elliotnash/OSU-ECE342-Oscilloscope/docs/blocks/frontend/frontend-portrait.png

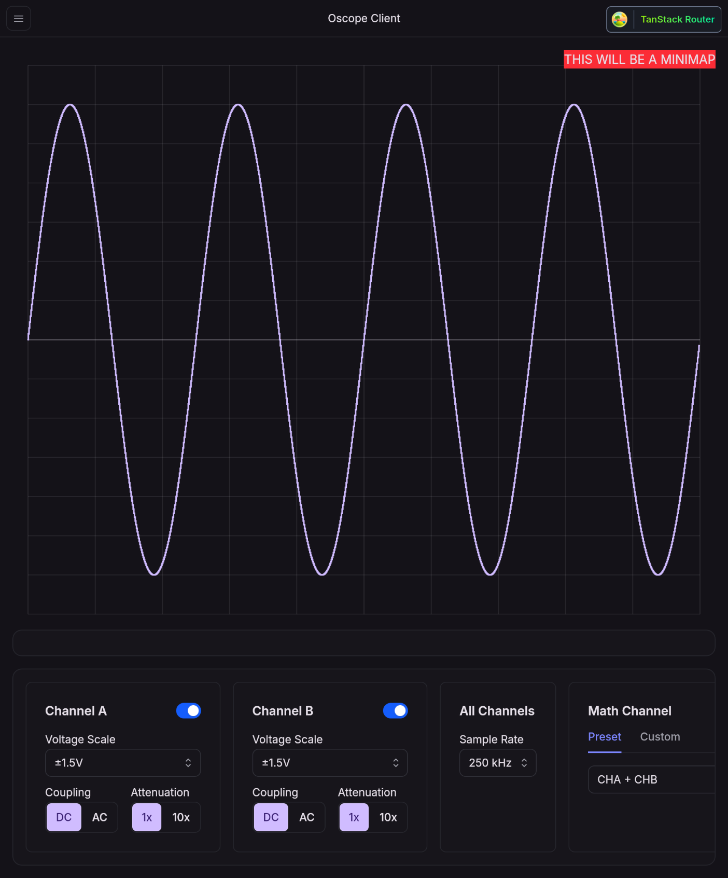
docs/blocks/frontend/frontend-portrait.png
