elliotnash/OSU-ECE342-Oscilloscope/docs/images/cover.jpeg

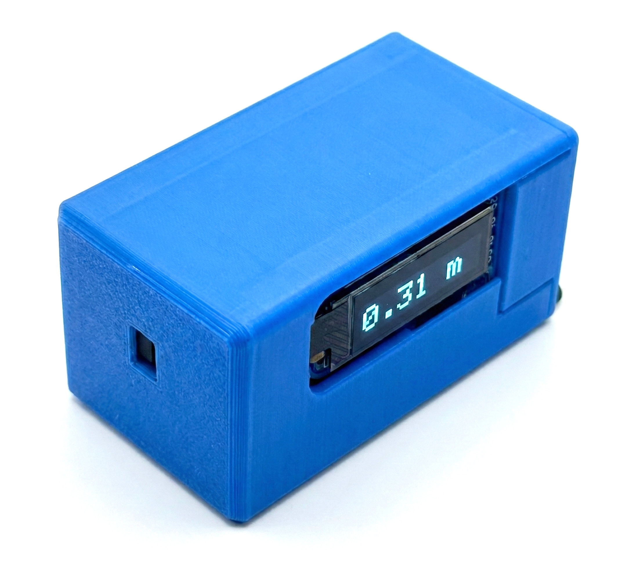
docs/images/cover.jpeg
