elliotnash/OSU-ECE342-Oscilloscope/docs/images/OscopeCaseTop.png

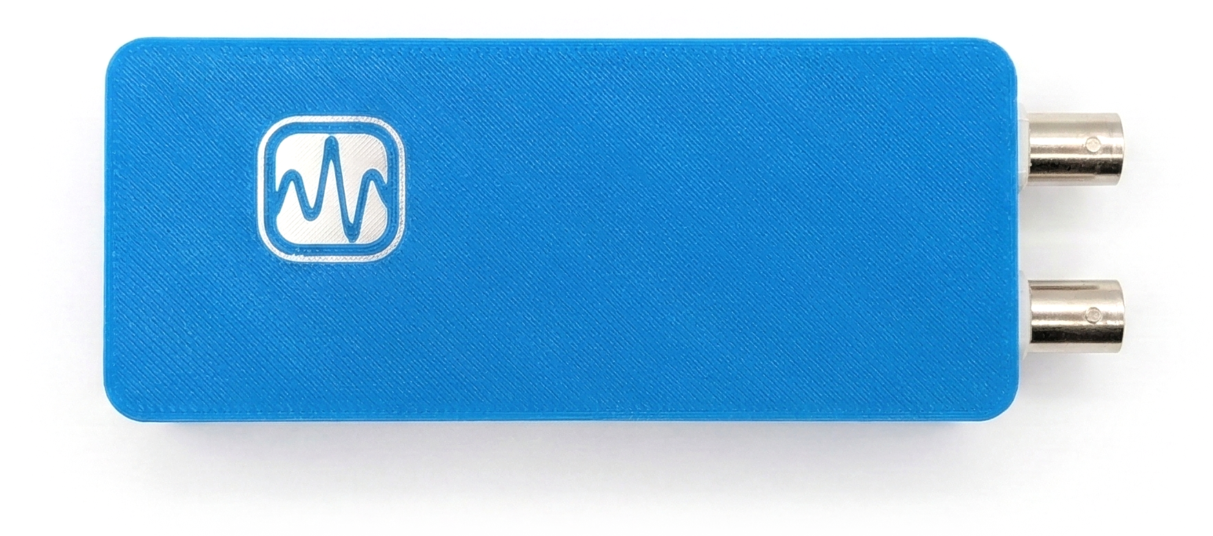
docs/images/OscopeCaseTop.png
