elliotnash/OSU-ECE342-Oscilloscope/docs/images/skeleton.jpeg

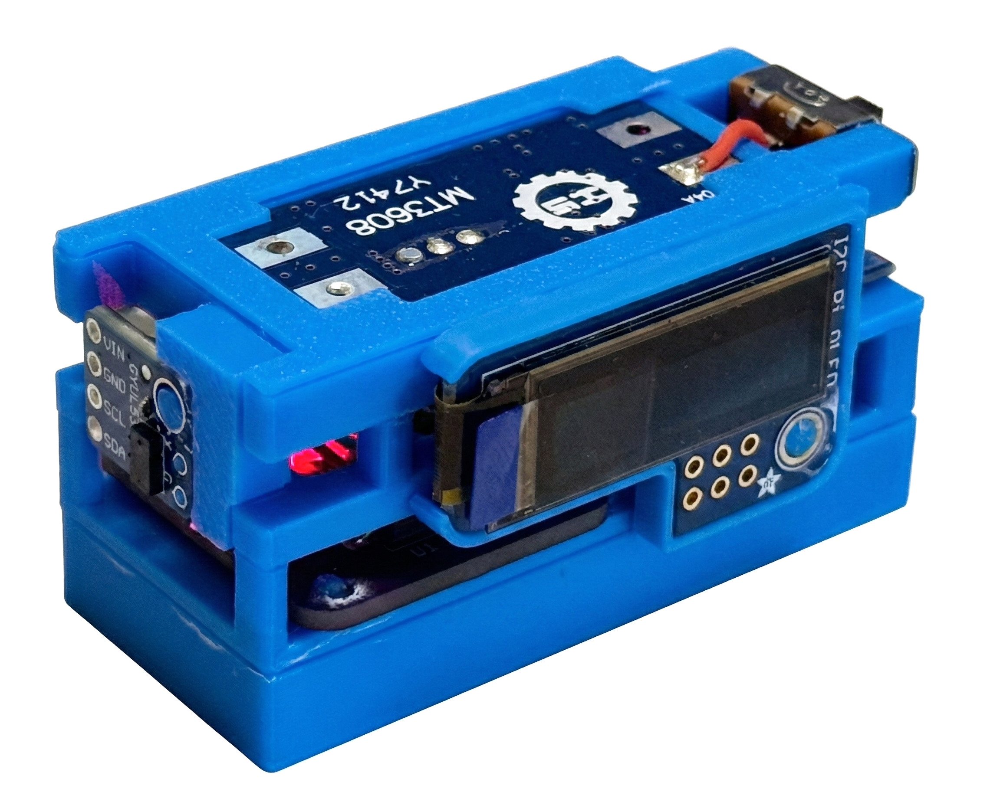
docs/images/skeleton.jpeg
