elliotnash/OSU-ECE342-Oscilloscope/docs/images/External Assembly.png

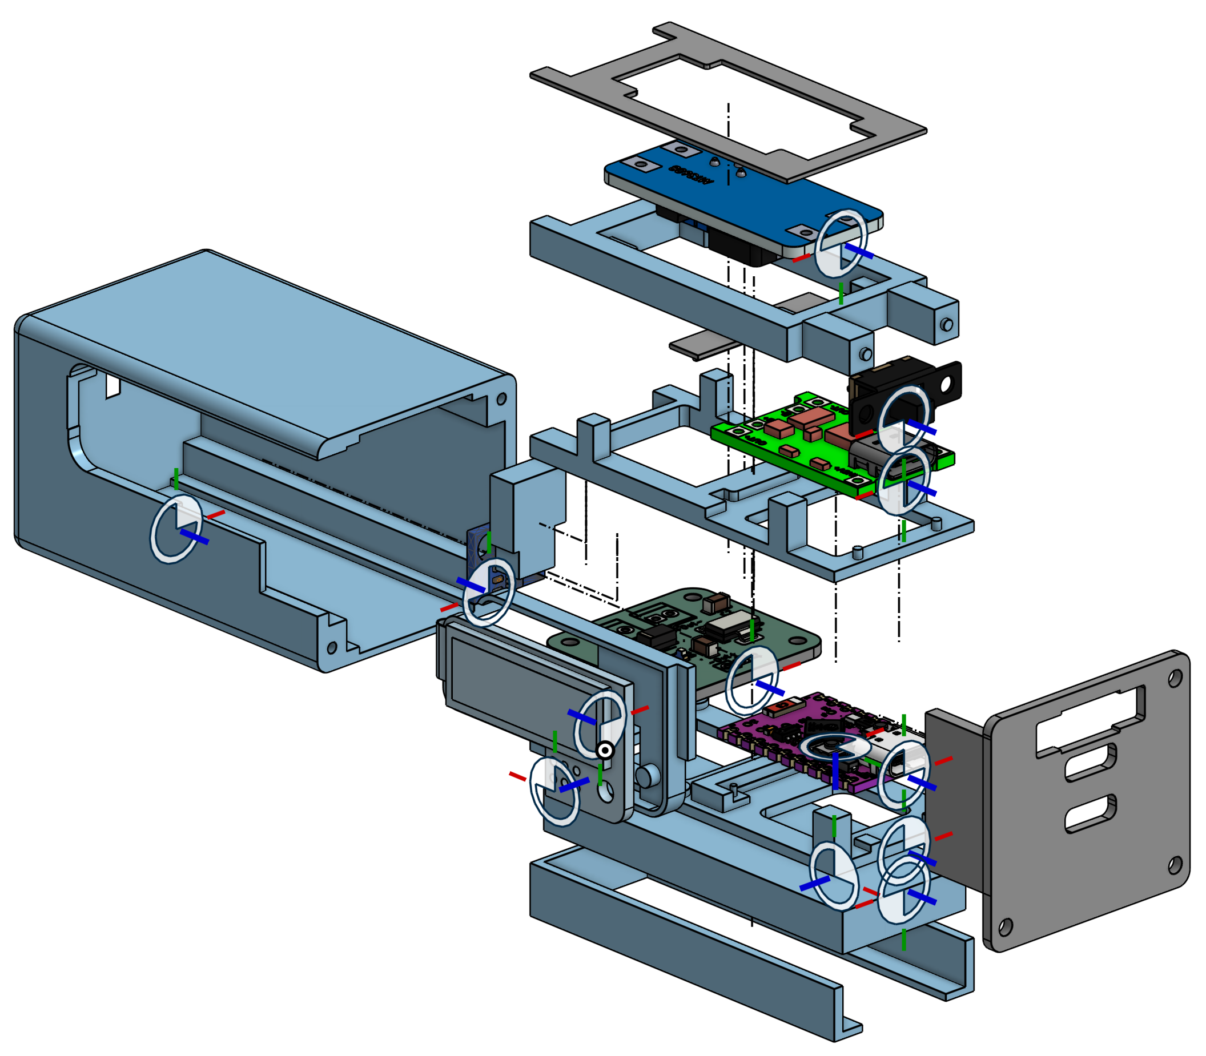
docs/images/External Assembly.png
